Magiclxw/HelloFinger/2.Firmware/HelloFinger/Core/Inc/gpio.h

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
/* Define to prevent recursive inclusion -------------------------------------*/
#ifndef __GPIO_H__
#define __GPIO_H__

#ifdef __cplusplus
extern "C" {
#endif

/* Includes ------------------------------------------------------------------*/
#include "main.h"

/* USER CODE BEGIN Includes */
typedef int(*FUNC_ACTIONKEYRECVTCB)(void);
typedef int(*FUNC_NORMALKEYRECVTCB)(void);
typedef int(*FUNC_JOYCONKEYRECVTCB)(void);
/* USER CODE END Includes */

/* USER CODE BEGIN Private defines */

//GPIOA
#define MCU_GPIO_JOYCON_KEY_PIN	GPIO_PIN_0
#define MCU_GPIO_ENCODER_KEY_PIN	GPIO_PIN_1
#define MCU_GPIO_TOUCH_PIN	GPIO_PIN_4
#define MCU_GPIO_KEY1_PIN	GPIO_PIN_8
#define MCU_GPIO_KEY0_PIN	GPIO_PIN_11
#define MCU_GPIO_CH9329_RESET_PIN	GPIO_PIN_12

//GPIOB
#define MCU_GPIO_CH9329_SET_PIN	GPIO_PIN_5
#define MCU_GPIO_ENCODER_SIGNAL_A	GPIO_PIN_6
#define MCU_GPIO_ENCODER_SIGNAL_B	GPIO_PIN_7
#define MCU_GPIO_KEY2_PIN	GPIO_PIN_14
#define MCU_GPIO_KEY3_PIN	GPIO_PIN_13

//GPIOC



/* USER CODE END Private defines */

void MX_GPIO_Init(void);
int RegisterActionKeyCallBack(FUNC_ACTIONKEYRECVTCB ACTIONRECVCBT);
int RegisterNormalKeyCallBack(FUNC_NORMALKEYRECVTCB NORMALKEYRECVCBT);
int RegisterJoyconKeyCallBack(FUNC_JOYCONKEYRECVTCB JOYCONKEYRECVCBT);
#ifdef __cplusplus
}
#endif
#endif /*__ GPIO_H__ */
