Magiclxw/HelloFinger/3.Software/HelloFinger/HelloFinger/form_mainwindow.h

#ifndef FORM_MAINWINDOW_H
#define FORM_MAINWINDOW_H

#include <QMainWindow>
#include <QSystemTrayIcon>
#include "msg_handler.h"
#include "hid_function.h"

QT_BEGIN_NAMESPACE
namespace Ui { class Form_MainWindow; }
QT_END_NAMESPACE

#define ADD_FINGER_PARAM_LED_ON 0x01
#define ADD_FINGER_PARAM_PRE_DISPOSE    0x02    //开启预处理
#define ADD_FINGER_PARAM_RETURN_KEY_PROCESS 0x04    //返回关键步骤
#define ADD_FINGER_PARAM_ID_COVER_ENABLE    0x08    //id允许覆盖
#define ADD_FINGER_PARAM_ENROLL_REPEAT_DISABLE  0x10    //不允许指纹重复注册
#define ADD_FINGER_PARAM_ENROLL_FINGER_NO_LEAVE    0x20    //注册过程不要求手指离开

#define HIDEWINDOW_HOLD_TIME    5000

class Form_MainWindow : public QMainWindow
{
    Q_OBJECT

public:
    uint8_t Set_color_R;
    uint8_t Set_color_G;
    uint8_t Set_color_B;
    Form_MainWindow(QWidget *parent = nullptr);
    ~Form_MainWindow();
    void on_keyEvent(QKeyEvent* event);
    void File_Update_TableContent(QString path);
    void File_Save_Shortcut();
    void Update_QuickStart_Content();
    void Update_HideWindow_List();
    void Chat_RevMsg_Handler(QString msg);
private:
    Ui::Form_MainWindow *ui;
    QSystemTrayIcon *m_sysTrayIcon;

    void InitSysTray();
    QMenu *m_menu;
    QAction *m_shoWindow;
    QAction *m_exit;
    void createAction();
    void createMenu();

protected:
    void dragEnterEvent(QDragEnterEvent *event) override;
    void dropEvent(QDropEvent *event) override;
    void closeEvent (QCloseEvent *event) override;

public slots:
    void Slot_AddFinger(void);
    void Slot_EnrollState(uint8_t state1,uint8_t state2);
    void Slot_DeleteFinger(void);
    void Slot_RefreshFinger(void);
    void Slot_UpdateIndexTable(void);
    void Slot_SetWindowsPassword(void);
    void Slot_SetPassword(void);
    void Slot_SetAccount_Password(void);
    void Slot_SetQuickStart(QUICK_START_e startID);
    void Slot_SetBreathRGB(void);
    void Slot_RGB_Display(void);
    void Slot_ChangeItemValue(void);
    void Slot_SaveItemValue(void);
    void Slot_SetShortcut(void);
    void Slot_DeleteListWidgetItem(void);
    void Slot_Chat_Send_Msg(void);
    void Slot_SetFingerRGB(void);
    void Slot_Popup_ChatSettingWindow(void);
    void Slot_Update_FirmwareMsg(char* date,char* version);
    void Slot_Update_HardwareMsg(uint8_t* flashId,char ch9329_ver,char* fpm383cSN);
signals:
    void Signal_AddFinger(uint8_t pos,uint8_t times,uint8_t param1,uint8_t param2);
    void Signal_DeleteFinger(uint8_t id);
    void Signal_RefreshFinger(void);
    void Signal_UpdateIndexTable(void);
    void Signal_SetWindowsPassword(QString password,uint8_t fingertype,uint8_t index);
    void Signal_SetPassword(QString password,uint8_t fingertype,uint8_t index);
    void Signal_SetAccount_Password(QString account,QString password,uint8_t fingertype,uint8_t index);
    void Signal_SetQuickStart(uint8_t fingertype,QUICK_START_e startID,uint8_t index);
    void Signal_SetBreathRGB(uint8_t color_R,uint8_t color_G,uint8_t color_B,uint8_t interval);
    void Signal_SetShortcut(uint8_t fingertype,uint8_t func,char* key,uint8_t key_len,uint8_t index);
    void Signal_UpdateHideWindowCheckedItem(int dir);
    void Signal_SetActionFunc(uint8_t func ,uint8_t action);
    void Signal_SetFingerRGB(uint8_t mode,uint8_t startColor,uint8_t stopColor,uint8_t interval);
    void Signal_OpenHidewindowItem(void);
    void Signal_GetFirmwareMsg(void);
    void Signal_GetHardwareMsg(void);
private slots:
    void Slot_ShowWindow();
    void Slot_Exit();
    void on_listWidget_task_1_customContextMenuRequested(const QPoint &pos);
    void on_listWidget_table_state_customContextMenuRequested(const QPoint &pos);
    void on_listWidget_task_2_customContextMenuRequested(const QPoint &pos);
    void on_listWidget_task_3_customContextMenuRequested(const QPoint &pos);
    void on_listWidget_task_4_customContextMenuRequested(const QPoint &pos);
    void on_listWidget_task_5_customContextMenuRequested(const QPoint &pos);
    void on_listWidget_table_state_key_customContextMenuRequested(const QPoint &pos);
    void on_listWidget_task_6_customContextMenuRequested(const QPoint &pos);
    void on_listWidget_hidwindow_customContextMenuRequested(const QPoint &pos);
    void on_pushButton_chat_copy_answer_clicked();
    void on_pushButton_action_play_pause_clicked();
    void on_pushButton_action_calculator_clicked();
    void on_pushButton_action_chat_clicked();
    void on_pushButton_action_computer_clicked();
    void on_pushButton_action_email_clicked();
    void on_pushButton_action_explorer_clicked();
    void on_pushButton_action_mute_clicked();
    void on_pushButton_action_power_clicked();
    void on_pushButton_action_screen_save_clicked();
    void on_pushButton_action_sleep_clicked();
    void on_pushButton_action_weakup_clicked();
    void on_pushButton_RGB_next_page_clicked();

    void on_pushButton_RGB_last_page_clicked();
    void on_pushButton_get_hardware_msg_clicked();
    void on_pushButton_get_firmware_msg_clicked();
    void on_pushButton_update_clicked();
};
#endif // FORM_MAINWINDOW_H
