Magiclxw/HelloFinger/2.Firmware/HelloFinger/Core/Src/usart.c

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
/* Includes ------------------------------------------------------------------*/
#include "usart.h"

/* USER CODE BEGIN 0 */
#include "stdio.h"
#include "sys_config.h"

#if 1

#if (__ARMCC_VERSION >= 6010050)            /* 使用AC6编译器时 */
__asm(".global __use_no_semihosting\n\t");  /* 声明不使用半主机模式 */
__asm(".global __ARM_use_no_argv \n\t");    /* AC6下需要声明main函数为无参数格式，否则部分例程可能出现半主机模式 */

#else
/* 使用AC5编译器时, 要在这里定义__FILE 和 不使用半主机模式 */
#pragma import(__use_no_semihosting)

struct __FILE
{
    int handle;
    /* Whatever you require here. If the only file you are using is */
    /* standard output using printf() for debugging, no file handling */
    /* is required. */
};

#endif

/* 不使用半主机模式，至少需要重定义_ttywrch\_sys_exit\_sys_command_string函数,以同时兼容AC6和AC5模式 */
int _ttywrch(int ch)
{
    ch = ch;
    return ch;
}

/* 定义_sys_exit()以避免使用半主机模式 */
void _sys_exit(int x)
{
    x = x;
}

char *_sys_command_string(char *cmd, int len)
{
    return NULL;
}


/* FILE 在 stdio.h里面定义. */
FILE __stdout;

/* MDK下需要重定义fputc函数, printf函数最终会通过调用fputc输出字符串到串口 */
int fputc(int ch, FILE *f)
{
    while ((USART3->SR & 0X40) == 0);     /* 等待上一个字符发送完成 */

    USART3->DR = (uint8_t)ch;             /* 将要发送的字符 ch 写入到DR寄存器 */
    return ch;
}
#endif

FUNC_USARTRECVTCB USART1RECVCallback = NULL;
FUNC_USARTRECVTCB USART2RECVCallback = NULL;
/* USER CODE END 0 */

UART_HandleTypeDef huart1;
UART_HandleTypeDef huart2;
UART_HandleTypeDef huart3;

/* USART1 init function */

void MX_USART1_UART_Init(void)
{

  huart1.Instance = USART1;
  huart1.Init.BaudRate = 9600;
  huart1.Init.WordLength = UART_WORDLENGTH_8B;
  huart1.Init.StopBits = UART_STOPBITS_1;
  huart1.Init.Parity = UART_PARITY_NONE;
  huart1.Init.Mode = UART_MODE_TX_RX;
  huart1.Init.HwFlowCtl = UART_HWCONTROL_NONE;
  huart1.Init.OverSampling = UART_OVERSAMPLING_16;
  if (HAL_UART_Init(&huart1) != HAL_OK)
  {
    Error_Handler();
  }
  /* USER CODE BEGIN USART1_Init 2 */
	__HAL_UART_ENABLE_IT(&huart1,UART_IT_RXNE);
  /* USER CODE END USART1_Init 2 */

}
/* USART2 init function */

void MX_USART2_UART_Init(void)
{

  huart2.Instance = USART2;
  huart2.Init.BaudRate = 57600;
  huart2.Init.WordLength = UART_WORDLENGTH_8B;
  huart2.Init.StopBits = UART_STOPBITS_2;
  huart2.Init.Parity = UART_PARITY_NONE;
  huart2.Init.Mode = UART_MODE_TX_RX;
  huart2.Init.HwFlowCtl = UART_HWCONTROL_NONE;
  huart2.Init.OverSampling = UART_OVERSAMPLING_16;
  if (HAL_UART_Init(&huart2) != HAL_OK)
  {
    Error_Handler();
  }
  /* USER CODE BEGIN USART2_Init 2 */
	__HAL_UART_ENABLE_IT(&huart2,UART_IT_RXNE);
  /* USER CODE END USART2_Init 2 */

}

void MX_USART3_UART_Init(void)
{

  huart3.Instance = USART3;
  huart3.Init.BaudRate = 115200;
  huart3.Init.WordLength = UART_WORDLENGTH_8B;
  huart3.Init.StopBits = UART_STOPBITS_1;
  huart3.Init.Parity = UART_PARITY_NONE;
  huart3.Init.Mode = UART_MODE_TX_RX;
  huart3.Init.HwFlowCtl = UART_HWCONTROL_NONE;
  huart3.Init.OverSampling = UART_OVERSAMPLING_16;
  if (HAL_UART_Init(&huart3) != HAL_OK)
  {
    Error_Handler();
  }
  /* USER CODE BEGIN USART2_Init 2 */
	__HAL_UART_ENABLE_IT(&huart3,UART_IT_RXNE);
  /* USER CODE END USART2_Init 2 */

}

void HAL_UART_MspInit(UART_HandleTypeDef* uartHandle)
{

  GPIO_InitTypeDef GPIO_InitStruct = {0};
  if(uartHandle->Instance==USART1)
  {
    /* USART1 clock enable */
    __HAL_RCC_USART1_CLK_ENABLE();

    __HAL_RCC_GPIOA_CLK_ENABLE();
    /**USART1 GPIO Configuration
    PA9     ------> USART1_TX
    PA10     ------> USART1_RX
    */
    GPIO_InitStruct.Pin = GPIO_PIN_9;
    GPIO_InitStruct.Mode = GPIO_MODE_AF_PP;
    GPIO_InitStruct.Speed = GPIO_SPEED_FREQ_HIGH;
    HAL_GPIO_Init(GPIOA, &GPIO_InitStruct);

    GPIO_InitStruct.Pin = GPIO_PIN_10;
    GPIO_InitStruct.Mode = GPIO_MODE_INPUT;
    GPIO_InitStruct.Pull = GPIO_NOPULL;
    HAL_GPIO_Init(GPIOA, &GPIO_InitStruct);

  /* USER CODE BEGIN USART1_MspInit 1 */
		HAL_NVIC_SetPriority(USART1_IRQn, 6, 0);
    HAL_NVIC_EnableIRQ(USART1_IRQn);
  /* USER CODE END USART1_MspInit 1 */
  }
  else if(uartHandle->Instance==USART2)
  {
    /* USART2 clock enable */
    __HAL_RCC_USART2_CLK_ENABLE();

    __HAL_RCC_GPIOA_CLK_ENABLE();
    /**USART2 GPIO Configuration
    PA2     ------> USART2_TX
    PA3     ------> USART2_RX
    */
    GPIO_InitStruct.Pin = GPIO_PIN_2;
    GPIO_InitStruct.Mode = GPIO_MODE_AF_PP;
    GPIO_InitStruct.Speed = GPIO_SPEED_FREQ_HIGH;
    HAL_GPIO_Init(GPIOA, &GPIO_InitStruct);

    GPIO_InitStruct.Pin = GPIO_PIN_3;
    GPIO_InitStruct.Mode = GPIO_MODE_INPUT;
    GPIO_InitStruct.Pull = GPIO_NOPULL;
    HAL_GPIO_Init(GPIOA, &GPIO_InitStruct);

  /* USER CODE BEGIN USART2_MspInit 1 */
		HAL_NVIC_SetPriority(USART2_IRQn, 5, 0);
    HAL_NVIC_EnableIRQ(USART2_IRQn);
  /* USER CODE END USART2_MspInit 1 */
  }
	else if(uartHandle->Instance==USART3)
  {
    /* USART2 clock enable */
    __HAL_RCC_USART3_CLK_ENABLE();

    __HAL_RCC_GPIOB_CLK_ENABLE();

    GPIO_InitStruct.Pin = GPIO_PIN_10;
    GPIO_InitStruct.Mode = GPIO_MODE_AF_PP;
    GPIO_InitStruct.Speed = GPIO_SPEED_FREQ_HIGH;
    HAL_GPIO_Init(GPIOB, &GPIO_InitStruct);

    GPIO_InitStruct.Pin = GPIO_PIN_11;
    GPIO_InitStruct.Mode = GPIO_MODE_INPUT;
    GPIO_InitStruct.Pull = GPIO_NOPULL;
    HAL_GPIO_Init(GPIOB, &GPIO_InitStruct);

  /* USER CODE BEGIN USART2_MspInit 1 */
		//HAL_NVIC_SetPriority(USART3_IRQn, 6, 0);
    //HAL_NVIC_EnableIRQ(USART3_IRQn);
  /* USER CODE END USART2_MspInit 1 */
  }
}

void HAL_UART_MspDeInit(UART_HandleTypeDef* uartHandle)
{

  if(uartHandle->Instance==USART1)
  {
    /* Peripheral clock disable */
    __HAL_RCC_USART1_CLK_DISABLE();

    /**USART1 GPIO Configuration
    PA9     ------> USART1_TX
    PA10     ------> USART1_RX
    */
    HAL_GPIO_DeInit(GPIOA, GPIO_PIN_9|GPIO_PIN_10);

  }
  else if(uartHandle->Instance==USART2)
  {
    /* Peripheral clock disable */
    __HAL_RCC_USART2_CLK_DISABLE();

    /**USART2 GPIO Configuration
    PA2     ------> USART2_TX
    PA3     ------> USART2_RX
    */
    HAL_GPIO_DeInit(GPIOA, GPIO_PIN_2|GPIO_PIN_3);

  }
}

/* USER CODE BEGIN 1 */
int RegisterUsart1ReceiveCallBack(FUNC_USARTRECVTCB USART1RECVCBT)
{
	USART1RECVCallback = USART1RECVCBT;
	return OPERATE_SUCCESS;
}

int RegisterUsart2ReceiveCallBack(FUNC_USARTRECVTCB USART2RECVCBT)
{
	USART2RECVCallback = USART2RECVCBT;
	return OPERATE_SUCCESS;
}
/* USER CODE END 1 */
