Magiclxw/HelloFinger/2.Firmware/HelloFinger/SYSTEM/sys/sys.h

#ifndef __SYS_H
#define __SYS_H

#include "stm32f1xx.h"

/**
 * SYS_SUPPORT_OS用于定义系统文件夹是否支持OS
 * 0,不支持OS
 * 1,支持OS
 */
#define SYS_SUPPORT_OS          1

#define Firmware_Version	 "1.0.0_beta"

typedef struct _SYSTEM_INFO_
{
	char *compile_date;
	char *compile_time;
	char firmware_version[10];
}_SYSTEM_INFO_t;

typedef struct JOYSTICK_INIT_PARAM_
{
	uint8_t JOYSTICK_INIT_PARAM_MIN_OFFSET;
	uint8_t JOYSTICK_INIT_PARAM_MAX_OFFSET;
	uint16_t JOYSTICK_INIT_PARAM_DEFAULT_LOW_THRESHOLD;
	uint16_t JOYSTICK_INIT_PARAM_DEFAULT_HIGH_THRESHOLD;
}JOYSTICK_INIT_PARAM_t;

typedef struct CH9329_INIT_PARAM_
{
	uint8_t CH9329_ADDR;
	uint8_t CH9329_BAUD[4];
}CH9329_INIT_PARAM_t;

typedef struct FPM383_INIT_PARAM_
{
	uint8_t FPM383_INIT_PARAM_ADDR[4];
	uint8_t FPM383_Password[4];
	uint8_t FPM383_RGB_func;
	uint8_t FPM383_RGB_startColor;
	uint8_t FPM383_RGB_stopColor;
	uint8_t FPM383_RGB_cycle;
	
}FPM383_INIT_PARAM_t;

typedef struct RGB_INIT_PARAM_
{
	float RGB_INIT_PARAM_R;
	float RGB_INIT_PARAM_G;
	float RGB_INIT_PARAM_B;
	float RGB_R_decrease;
	float RGB_G_decrease;
	float RGB_B_decrease;
	uint8_t RGB_interval;
	
}RGB_INIT_PARAM_t;

typedef struct SYSTEM_INIT_PARAM_
{
	JOYSTICK_INIT_PARAM_t joystick_param;
	CH9329_INIT_PARAM_t ch9329_param;
	FPM383_INIT_PARAM_t fp383_param;
	RGB_INIT_PARAM_t rgb_param;
}SYSTEM_INIT_PARAM_t;

typedef struct 
{
	uint8_t CH9329_INFO[3];
	uint8_t W25Q128_INFO[2];
	uint8_t FPM383C_INFO[32];
}SYSTEM_HARDWARE_INFO_t;


void Task_Create(void);
int System_PARAM_Init(void);
void SYSTEM_Init(void);
#endif
