Magiclxw/HelloFinger/2.Firmware/HelloFinger/USER/application/app_task_hid_transfer.h

#ifndef __APP_TASK_HID_TRANSFER_H
#define __APP_TASK_HID_TRANSFER_H
#include "sys_config.h"
#include "sys.h"
#include "drv_ch9329.h"

#define KEY_CMD_HEAD_H	(0x57)
#define KEY_CMD_HEAD_L	(0xAB)
#define KEY_CMD_ADDR		(0x00)

#define CRC_LEN	(4)

#define TASK_KEY_CONTROL_SIZE	(200)
#define TASK_KEY_CONTROL_PRIORITY	(5)

#define KEY_DATA_HANDLE_QUEUE_LEN	(3)
#define KEY_DATA_HANDLE_QUEUE_SIZE	(1)
#define COMPUTER_INFO_QUEUE_LEN	(1)
#define COMPUTER_INFO_QUEUE_SIZE	(1)

typedef enum USB_PROTOCOL_FORMAT
{
    USB_PROTOCOL_FORMAT_NOUSE0,				  //0x00
    USB_PROTOCOL_FORMAT_MODE_SWITCH,		  //0x01
    USB_PROTOCOL_FORMAT_GET_FW,            //0x02	获取固件信息
    USB_PROTOCOL_FORMAT_GET_HW,               //0x03	获取硬件信息
    USB_PROTOCOL_FORMAT_NOUSE3,               //0x04
    USB_PROTOCOL_FORMAT_NOUSE4,               //0x05
    USB_PROTOCOL_FORMAT_NOUSE5,               //0x06
    USB_PROTOCOL_FORMAT_NOUSE6,               //0x07
    USB_PROTOCOL_FORMAT_NOUSE7,               //0x08
    USB_PROTOCOL_FORMAT_NOUSE8,               //0x09
    USB_PROTOCOL_FORMAT_NOUSE9,               //0x0A
    USB_PROTOCOL_FORMAT_ENROLL_FINGER,        //0x0B
    USB_PROTOCOL_FORMAT_DELETE_FINGER,    	  //0x0C
    USB_PROTOCOL_FORMAT_SET_FINGER_COLOR,     //0x0D
    USB_PROTOCOL_FORMAT_NOUSE11,			  //0x0E
    USB_PROTOCOL_FORMAT_SET_FINGER_COLOR_PRO, //0x0F
    USB_PROTOCOL_FORMAT_GET_INDEX_LIST,		  //0x10
    USB_PROTOCOL_FORMAT_FUNC_STORE,           //0x11
    USB_PROTOCOL_FORMAT_SET_RGB,              //0x12
		USB_PROTOCOL_FORMAT_SET_ACTION,						//0x13	设置Action按键功能
}USB_PROTOCOL_FORMAT_e;



typedef enum{
    TYPE_Windows_Password = 0,
    TYPE_Password,
    TYPE_Account_Password,
    TYPE_Shortcut,
		TYPE_QuickStart,
    TYPE_KEY_Windows_Password,
    TYPE_KEY_Password,
    TYPE_KEY_Account_Password,
    TYPE_KEY_Shortcut,
		TYPE_KEY_QuickStart,
}CMD_TYPE_e;

typedef struct KEY_DATA_CONTROLLER
{
	volatile uint8_t *pData;
	volatile uint8_t rec_data_size;
	volatile DATA_RECV_STATE_e head_state_H;
	volatile DATA_RECV_STATE_e head_state_L;
	volatile DATA_RECV_STATE_e addr_state;
	volatile DATA_RECV_STATE_e data_state;	//开始接收数据标志
	volatile uint16_t data_length;
}KEY_DATA_CONTROLLR_t;

typedef struct KEY_DATA_FORMAT
{
	volatile uint8_t head[2];
	volatile uint8_t addr;
	volatile uint8_t cmd;
	volatile uint8_t len;
	volatile uint8_t data[CH9329_TRANS_MAX_DATA_LEN];
	volatile uint8_t sum;	//sum = head[0] + head[1] + addr + cmd + len + data[...]
}KEY_DATA_FORMAT_t;

int HID_Data_Handle(void);
int Key_GiveNotifyFromISR(uint8_t *recData,uint8_t dataSize);
int Task_Key_DataCTLCreate(void);

#endif
