Magiclxw/HelloFinger/2.Firmware/HelloFinger/Core/Src/dma.c

#include "dma.h"

void MX_DMA_Init(void)
{

  /* DMA controller clock enable */
  __HAL_RCC_DMA1_CLK_ENABLE();

  /* DMA interrupt init */
  /* DMA1_Channel1_IRQn interrupt configuration */
  HAL_NVIC_SetPriority(DMA1_Channel1_IRQn, 6, 0);
  HAL_NVIC_EnableIRQ(DMA1_Channel1_IRQn);
	
	HAL_NVIC_SetPriority(DMA1_Channel2_IRQn, 6, 0);
  HAL_NVIC_EnableIRQ(DMA1_Channel2_IRQn);
	
  HAL_NVIC_SetPriority(DMA1_Channel3_IRQn, 6, 0);
  HAL_NVIC_EnableIRQ(DMA1_Channel3_IRQn);
	
	HAL_NVIC_SetPriority(DMA1_Channel5_IRQn, 6, 0);
  HAL_NVIC_EnableIRQ(DMA1_Channel5_IRQn);
}
