Magiclxw/HelloFinger/2.Firmware/HelloFinger/Core/Inc/usart.h

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
/* Define to prevent recursive inclusion -------------------------------------*/
#ifndef __USART_H__
#define __USART_H__

#ifdef __cplusplus
extern "C" {
#endif

/* Includes ------------------------------------------------------------------*/
#include "main.h"

/* USER CODE BEGIN Includes */
#include "stdio.h"
/* USER CODE END Includes */

extern UART_HandleTypeDef huart1;

extern UART_HandleTypeDef huart2;

extern UART_HandleTypeDef huart3;

/* USER CODE BEGIN Private defines */
#define KEY_HANDLE		huart1
#define FINGER_HANDLE	huart2
#define DEBUG_HANDLE	huart3

typedef int(*FUNC_USARTRECVTCB)(uint8_t *pData, uint8_t Datasize);//串口接收回调函数指针定义
/* USER CODE END Private defines */

void MX_USART1_UART_Init(void);
void MX_USART2_UART_Init(void);
void MX_USART3_UART_Init(void);

/* USER CODE BEGIN Prototypes */
int RegisterUsart1ReceiveCallBack(FUNC_USARTRECVTCB USART1RECVCBT);
int RegisterUsart2ReceiveCallBack(FUNC_USARTRECVTCB USART2RECVCBT);
/* USER CODE END Prototypes */

#ifdef __cplusplus
}
#endif

#endif /* __USART_H__ */
